aclandmark/PCB-111000_V2/9_Nano_Projects/7_Timers/7G_2_Combined_clock_SW/7G_2_Combined_clock_SW.ino

/*Proj_7G_Combined_clock_SW
***********************************************************/

/*IT INTRODUCES


  1.  A crystal controlled clock/Stop Watch application.

  Timing is provided using a 10mS I2C interrupt provided by the mini-OS that puts all clock/SW features under the
  control of the "Project_SW".
  The UNO clock has been found accurrate to about 1% which is not really adequate for monitoring the time.


  2.  An "atomic process".

  Elapsed time is recorded in seconds in a variable known as "sec_counter".  It is updated by a TWI ISR and processed
  by "main" and other subroutines. If any of these processes were interrupted by the TWI ISR then "sec_counter" would
  get corrupted and the process would fail.
  A different variable "sec_counter_V" is therefore defined.   This is the variable that the ISR updates directly.
  Its value is copied to "sec_counter" at regular intervals. Global interrupts are disabled while this process is
  in progress, using the following code

  " cli(); sec_counter = sec_counter_V; sei();"

  3.  Project subroutine "I2C_initiate_10mS_ref();"

  This is used to initiate the 10mS TWI interrupt


  EEPROM USAGE

  address 2 Data entry mode   Time string entered manually or seconds read from EEPROM
  addresses 3-6 Time input by user in seconds
  addresses 7-10 Display time time in secs (Clock or SW)
  addresses 11-14 "clock time" in seconds: When a new SW is selected save the "sec_counter" in clock time and
  "reset sec_counter"
  address 15 clock_mode


  USER INSTRUCTIONS



  Connect to pc  Should get "R   R   R   R....." user prompt
  if not hold sw2 down and reset.
  Keypress R gives the user insructions
  press sw3 get message enter time
  Enter time 24 hour clock
  Power cycle to 5V supply if wanted
  press sw3 then sw1 to start
  press sw1 to toggle between clock and new SW
  press sw2 to restore old SW
  press sw3 to pause, blank and restore display
  At initial POR press sw2 (rather that sw3) to get two SW's

  To adjust time: Press SW1 to restore clock time
  Then immediately press SW3
  This will cause a WD time out
  Release sw1 to increment time
  sw2 to decrement time
  Both switches to restore normal operation.


  Switch location SW1(PD2) - SW2(PD7) - SW3(PB2)
  PD2&7 call ISR(PCINT2_vect)
  PB2 calls ISR(PCINT0_vect)
  ISR on SW2 is never used.*/

/*
  clock_mode is storred in EEPROM address 2: When  subroutine set_time() is called
    users enter time for a clock_mode of 255 and mode is set thzero so that
    time is read from the EEPROM for a clock_mode of zero
    Having entered time set clock mode to zero
*/




#include "Proj_7G_2_header_file_1.h"
#include "Proj_7G_2_header_file_2.h"

long clock_time_secs = 0;                            //Value is seconds: Backed up in EEPROM when SW is selected


int main (void) {

  int line_no[6] = {0x14, 0x8B, 0xDE,  0x10F, 0x15F, 0x1C4};

  long SW_resume_time = 0;                              //Value in seconds: Used when switching from clock to SW
  long clock_resume_time = 0;                          //Value is seconds: Used when switching from SW to clock time


  /*****************Normal program entry mode: Everything is OK********************************/
  if (Arduino_non_WDTout) {                           //EEPROM 0x3EE holds anything except zero
    clear_Arduino_WDT_flag;                             //set it to to 0xFF

    setup_HW_for_clock_SW;

    Timer_T1_sub(T1_delay_100ms);
    if ((switch_2_down) || (MCUSR & (1 << EXTRF)))
    { while (switch_2_down); clear_data_mode;              //Ensure that the user prompt is skipped
      Timer_T1_sub(T1_delay_100ms);
    }

    else set_data_mode;


    if (data_mode_not_set)                              //Goes here following POR
    {if (power_on_reset == 1)
    {power_on_reset = 0;User_prompt_A;}
      Serial.write("\r\n\r\nTo retrieve these instructions press -r-\
at the p/r prompt or POR with sw2 pressed.\r\n\r\n\
Press sw3 and enter time or sw2 to reset it to zero,\
then press sw1 to start the clock.\r\n");
      for (int m = 0; m < 6; m++)
        Read_user_instructions(line_no[m]);//Serial.write(message_1);
    }

    for (int m = 0; m <= 11; m++)
    {
      eeprom_write_byte((uint8_t*)(m + 7), 0); //clear BKP space
    }

    while (1) {
      if (switch_2_down)
      {
        clock_mode = 2;  //Select timer or clock
        break;
      }
      if (switch_3_down) {
        clock_mode = 1;
        break;
      }
    }
    while ((switch_3_down) || (switch_2_down));

    clock_time_secs = 0;
    old_clock_mode = 0;
    payload = 2;
  }



  /*****************WDT with interrupt sets "Arduino_WDTout" and is used to adjust time**********************/
  if (Arduino_WDTout) {                                     //Arduino_WDTout
    clear_Arduino_WDT_flag;

    setup_HW_for_clock_SW;

    sec_counter = eeprom_read_byte((uint8_t*)(10));           //Read saved value of sec_counter from EEPROM
    for (int m = 0; m < 3; m++) {
      sec_counter = (sec_counter << 8)
                    + eeprom_read_byte((uint8_t*)(9 - m));
    }

    if ((switch_3_down) && (switch_1_down)) {                 //User induced watch dog timeout:
      while ((switch_3_down) || (switch_1_down)) {              //Use sw_1 and sw_3 to adjust time
        if ((switch_3_up) && (switch_1_down)) {
          sec_counter += 1;
        }
        if ((switch_1_up) && (switch_3_down)) {
          sec_counter -= 1;
        }
        Timer_T0_10mS_delay_x_m(10);
        Calculate_time();
        digits[0] = '0'; digits[1] = '0';                         //Sets mS*10 to zero  masks mS*10
        I2C_Tx_8_byte_array(digits);
      }
    }                            //Displays time as adjusted by user

    clock_mode = eeprom_read_byte((uint8_t*)15);              //Obtain "mode" and "clock_time_secs" from EEPROM
    clock_time_secs = eeprom_read_byte((uint8_t*)(14));
    for (int m = 0; m < 3; m++) {
      clock_time_secs = (clock_time_secs << 8) +
                        eeprom_read_byte((uint8_t*)(13 - m));
    }

    sec_counter += 1;                                     //Fudge factor??
    clock_resume_time = sec_counter;
    sec_counter_V = sec_counter;                          //Volatile version of "sec_counter"
    ms_counter = 0;                                       //mSecs are not restored
    clock_time_long = clock_time_secs * 100;
    Calculate_time();
    payload = 8;                                          //After WDT out update display
    setup_64ms_WDT_with_interrupt;                        //Re-establish WDT
    I2C_initiate_10mS_ref(); sei();
  }                       //Reinitialise 10mS tick


  /**************************Normal program continues********************************/
  set_up_PCI;
  enable_PCI;

  disable_PCI_on_sw1;
  disable_PCI_on_sw2;
  display_clear = 0;

  while (1) {                                               //Main loop: Continuously cycles through this loop (every 188uS??).

    switch (clock_mode) {
      case 0: break;
      case 1: set_time();                                       //Clock mode: "set_time()" requests start time  & saves it in "sec_counter"
        clock_mode = 'A'; break;
      case 2: sec_counter = 0;                                  //SW mode: start at time zero
        clock_mode = 'A';
        set_data_mode;
        for (int m = 0; m <= 3; m++)                          //Clear EEPROM sec_counter value
        {
          eeprom_write_byte((uint8_t*)(m + 3), 0);
        }
        break;
      case 'A':
        ms_counter = 0;
        sec_counter_V = sec_counter;                           //Initialise sec_counter_V
        Calculate_time();                                      //Converts time in seconds to string (Hr,Min and Sec)
        digits[0] = '0'; digits[1] = '0';                      //Sets mS*10 to zero  masks mS*10
        I2C_Tx_8_byte_array(digits);                           //Displays time
        clock_resume_time = sec_counter;
        clock_mode = 'E';
        break;

      case 'E':                                               //Clock ready to start: Awaiting sw3 press
        if (switch_1_up); else {
          I2C_initiate_10mS_ref();                              //Initiate TWI interrupt (every 10mS)
          sei();
          clock_mode = 'B';
          setup_64ms_WDT_with_interrupt;
        }                       //User input finished: Start WDT
        break;

      case 'B': if (!(TWI_flag));
        else {
          TWI_flag = 0; Update_sec_counter;                  //Clock running mode
          old_clock_mode = 'B';
          if (((86400 + sec_counter - clock_resume_time) % 86400 > 1)
              && ((switch_2_down) || (switch_1_down)))
          { if (switch_1_down) {
              clock_time_secs =
                clockTOstop_watch(); clock_mode = 'F';
            }
            if (switch_2_down) {
              SW_resume_time =
                restore_stop_watch(); clock_mode = 'H';
            }
          }
          else Timer();
        }
        break;                                                   //Convert clock to stop watch

      case 'F': if (!(TWI_flag));
        else {
          TWI_flag = 0; Update_sec_counter;                  //Stop watch mode
          old_clock_mode = 'F';
          if (((sec_counter) > 1) && ((switch_1_down)))
          {
            clock_resume_time = restore_Clock();
            clock_mode = 'B';
          }
          else Timer();
        }
        break;                                                  //Restore clock

      case 'H': if (!(TWI_flag));
        else {
          TWI_flag = 0;   Update_sec_counter;               //Stop watch restored mode
          old_clock_mode = 'H';
          if (((86400 + sec_counter - SW_resume_time) % 86400 > 1) &&
              (switch_1_down))
          {
            clock_resume_time = restore_Clock();
            clock_mode = 'B';
          }
          else Timer();
        }
        break;

      case 'C':
        payload = 0; TWI_flag = 0;
        Update_sec_counter; break;                              //Stop watch/clock display paused: Tick continues

      case 'G':
        payload = 0; TWI_flag = 0; Update_sec_counter;
        if (!(display_clear)) clear_display(); break;           //blank display

      case 'D':
        TWI_flag = 0;
        restore_display();  clock_mode = old_clock_mode;       //Stop watch/clock display re-activated
        break;
    }

    Timer_T2_sub(T2_delay_2ms);
    wdr();
  }
}                                               //reset the watchdog


/*****************************************************************************************************************/
void Timer(void) {                                     //Calls "update_7_seg_display", to close one I2C transaction and sets "payload" to initiate the next one
  digits[1] = ms_counter / 10 + '0';                    //Calculate mS display MSB
  digits[0] = ms_counter % 10 + '0';                    //Calculate mS display LSB
  if (!((digits[0] == '0') && (digits[1] == '0')))      //For mS tick 0 to 99 only update mS display
  {
    update_7_seg_display(); //Update mS display
  }
  if (!(ms_counter % 100)) {                            //When 1 second tick occurs
    Calculate_time();                                     //Calculate time: Hr:Min:Sec
    update_7_seg_display();
  }                              //Update display and complete the current I2C transaction
  if (ms_counter == 99)payload = 8; else payload = 2;
}       //Set payload for next TWI_interrupt 8 for 1sec tick, 2 for 10mS tick


/*****************************************************************************************************************/
ISR(TWI_vect) {                                         //Detects 10mS interrupt. Initiates I2C_transaction and responds by sending payload size
  unsigned char Null_byte;
  TWI_flag = 1;                                           //Informs main loop that a 10mS tick has occurred
  ms_counter = (ms_counter + 1) % 100;                    //mS counter continuously cycles through 0 to 100
  if (!(ms_counter)) {
    sec_counter_V++;                     //Volatile version of "sec_counter" increments every second
    if (sec_counter_V == 86400)sec_counter_V = 0;           //Roll-over for 24 hour clock
    sec_counter_save = 1;
  }                                     //Enables "sec_counter" to be updated from "sec_counter_V"
  Null_byte =  TWDR;                                       //Detect slave address + slave transmit data command
  TWDR = payload;                                          //Transmit payload value
  TWCR = (1 << TWEN) | (1 << TWINT);                       //clear interrupt but no ack required Next byte will be the last
  while (!(TWCR & (1 << TWINT)));                          //Wait for TWINT flag
  if (!(payload))
    TWCR =
      (1 << TWINT) | (1 << TWEA) | (1 << TWEN) | (1 << TWIE);
} //No payload? Prepare for next 10ms interrupt


/*****************************************************************************************************************/
void update_7_seg_display(void) {
  unsigned char Null_byte;
  cli();                                                    //Pause twi interrupt
  hold_PCI_on_sw1_and_sw3;
  {
    digits[0] = digits[1];  //Optional: masks 10mS digit
    digits[1] = 0;
  }
  TWCR = (1 << TWINT) | (1 << TWEA) | (1 << TWEN);         //Enable slave mode and set Enable Acknowledge
  while (!(TWCR & (1 << TWINT)));                          //No interrupt: wait for comms from master
  Null_byte =  TWDR;                                       //Read slave adress
  for (int m = 0;  m < payload; m++) {
    TWDR = digits[m];                                         //Transmit data for display
    if (m == (payload - 1))TWCR = (1 << TWINT) | (1 << TWEN); //last byte being transmitted now expect NACK in response
    else {
      TWCR = (1 << TWINT) | (1 << TWEA) | (1 << TWEN); //ACK pulse normally required
    }
    while (!(TWCR & (1 << TWINT)));
  }                          //Clear interrupt
  TWCR =
    (1 << TWINT) | (1 << TWEA) | (1 << TWEN) | (1 << TWIE);   //Prepare for next 10ms interrupt
  restore_PCI_on_sw1_and_sw3;
  sei();
}                                                   //re-enable twi interrupt


/*****************************************************************************************************************/
void Calculate_time(void) {
  Hours = sec_counter / 3600;                               //Obtain hours 0 to 23
  Minutes = (sec_counter % 3600) / 60;                      //Obtain minutes
  Seconds = (sec_counter % 3600) % 60;                      //Obtain seconds
  timer_utoa(Hours); HoursH = charH; HoursL = charL;        //Convert hours to string
  timer_utoa(Minutes); MinsH = charH; MinsL = charL;       //Convert minutes to string
  timer_utoa(Seconds); SecsH = charH; SecsL = charL;
}     //Convert seconds to string


/*****************************************************************************************************************/
void set_time(void) {
  unsigned int Two_sec_counter;                             //Required because of difficulties combining long and char variables
  unsigned char data_mode;

  data_mode = eeprom_read_byte((uint8_t*)0x02);             //Read mode. Default value is 255
  switch (data_mode) {

    case 255:                                                  //Default mode: User enters time
      Serial.write("\r\nEnter start time Hours, Minutes and \
Seconds (24 hour clock, no spaces)\r\n");
      while (isCharavailable_A(50) == 0) {
        Serial.write("T?  ");
      }
      HoursH = Serial.read();
      while (isCharavailable_A(5) == 0); HoursL = Serial.read();
      while (isCharavailable_A(5) == 0); MinsH = Serial.read();
      while (isCharavailable_A(5) == 0); MinsL = Serial.read();
      while (isCharavailable_A(5) == 0); SecsH = Serial.read();
      while (isCharavailable_A(5) == 0); SecsL = Serial.read();
      msecsH = 0; msecsL = 0;
      Two_sec_counter = ((((HoursH - '0') * 10) + HoursL - '0') * 1800)\
                        + ((((MinsH - '0') * 10) + MinsL - '0') * 30) + ((SecsH - '0') * 10 + SecsL - '0') / 2;
      sec_counter = Two_sec_counter;
      sec_counter *= 2;
      if (((SecsH - '0') * 10 + SecsL - '0') % 2)sec_counter++;

      for (int m = 0; m <= 3; m++)
      { eeprom_write_byte((uint8_t*)(m + 3), sec_counter >> (m * 8));
        Timer_T0_sub(T0_delay_5ms);
      }
      set_data_mode;
      break;

    case 0:
      sec_counter = eeprom_read_byte((uint8_t*)(6));          //Read start time and place in sec_counter
      for (int m = 0; m < 3; m++) {
        sec_counter = (sec_counter << 8) +
                      eeprom_read_byte((uint8_t*)(5 - m));
      }
      clear_data_mode;  break;

    default: clear_data_mode;
      wdt_enable(WDTO_30MS);
      while (1); break;
  }
}                                          //Corrupt clock_mode variable: set to default value and restart


/*****************************************************************************************************************/
void timer_utoa(char n) {                                   //converts an unsigned number to a string of digits
  if (n >= 10)
  { charL = n % 10;
    charH = (n - charL) / 10;
    charL = charL + '0';
    charH = charH + '0';
  }
  else
  {
    charH = '0';
    charL = n + '0';
  }
}


/*****************************************************************************************************************/
ISR(PCINT2_vect) {                                          //PORTB switch_1 interrupts

  if (switch_3_up)return;                                     //Ignore interrupt on switch release
  if (switch_1_up) {                                          //User triggered WDTout to adjust clock

    switch (clock_mode) {
      case 0: clock_mode = 1; break;                             //Enter the start timer
      case 'H':
      case 'F':
      case 'B':  clock_mode = 'C'; break;                         //Mode B clock is running Mode C Display paused
      case 'C':  clock_mode = 'G'; break;
      case 'G':  clock_mode = 'D'; break;
    }
  }

  else

    if (clock_mode != 'B')return;
    else {
      payload = 8; sei(); while (1);
    }
}


/*****************************************************************************************************************/
long clockTOstop_watch(void) {                             //Saves time before selecting stop watch display (i.e. resetting time to zero)
  long clock_time_secs_L;
  clock_time_long = (sec_counter * 100) + ms_counter;       //Current time "secs*10 + ms" saved in global variable clock_time.
  ms_counter = 0;                                           //Reset msecs
  sec_counter = 0;                                          //Reset secs
  clock_time_secs_L = clock_time_long / 100;                //Ignore ms when saving clock time
  update_7_seg_display();                                   //Runs "update_7_seg_display()" to complete the current I2C transaction
  payload = 8;                                              //Set payload to 8 for full display update during next I2C transaction
  while (!(ms_counter));                                    //Wait for next interrupt ms_counter increments from 0 to 1
  TWI_flag = 0;                                             //Clear TWI_flag
  for (int m = 0; m <= 7; m++)digits[m] = '0';              //Clears all digits
  update_7_seg_display();                                   //Runs "update_7_seg_display()" to complete I2C transaction
  payload = 2;                                              //Payload of 2 required for next update
  cli(); sec_counter_V = 0; sei();                          //Update volatile version of the sec_counter and return to "main loop"
  return clock_time_secs_L;
}


/*****************************************************************************************************************/
long restore_Clock(void) {                                 //Restores time by adding "clock_time" to the current SW time
  long time, clock_restore_time;
  unsigned char x;
  time = (sec_counter * 100) + ms_counter +
         clock_time_long;                                           //Add saved "clock_time" to SW time to get current value of time
  sec_counter = time / 100;                                  //Calculate new value of "sec_counter" and "ms_counter"
  ms_counter = time % 100 - 2;                               //2mS fudge factor required for mseconds
  if (sec_counter >= 86400)sec_counter -= 86400;            //compensates for 24Hr roll-over
  update_7_seg_display();                                   //Run "update_7_seg_display()" to complete the current I2C transaction
  x = ms_counter;                                           //Record "ms_counter"
  clock_restore_time = sec_counter;                         //saves "sec_counter" in "clock_restore_time"
  Calculate_time();                                          //Calculate time Hr:Min:sec
  digits[1] = ms_counter / 10 + '0';                         //Calculate mS display MSB
  digits[0] = ms_counter % 10 + '0';                         //Calculate mS display LSB
  payload = 8;                                               //Sets the payload to 8 ahead of next I2C transaction (update full disdplay)
  while (ms_counter == x);                                   //Wait for next interrupt (ms_counter increments from x to x+1)
  TWI_flag = 0;                                              //Set TWI_flag to zero
  update_7_seg_display();                                    //Full display update (completes the current I2C transaction)
  if (ms_counter == 99)payload = 8; else payload = 2;        //Enables contiguous 8 digit updates when necessary
  cli(); sec_counter_V = sec_counter; sei();                 //Update volatile version of second_counter
  Serial.write("\r\n"); return clock_restore_time;
}          //Return "clock_restore_time" to "main loop"


/*****************************************************************************************************************/
long restore_stop_watch() {                               //Restores SW time by subtracting the current time from the value stored in "clock_time"
  unsigned long time, SW_restore_time;
  unsigned char x;
  time = 8640000 + (sec_counter * 100) +
         ms_counter - clock_time_long;                            //Computes the updated value of SW time
  if (time >= 8640000) time -= 8640000;                    //Compensate for 24 Hr roll-over
  sec_counter = time / 100;                                //Calculate new value of "sec_counter" and "ms_counter"
  ms_counter = time % 100 - 2;                             //2mS fudge factor required for mseconds
  update_7_seg_display();                                  //Run "update_7_seg_display()" to complete the current I2C transaction
  x = ms_counter;                                          //Record "ms_counter"
  SW_restore_time = sec_counter;                           //saves "sec_counter" in "SW_restore_time"
  Calculate_time();                                        //Calculate time Hr:Min:sec
  digits[1] = ms_counter / 10 + '0';                       //Calculate mS display MSB
  digits[0] = ms_counter % 10 + '0';                       //Calculate mS display LSB
  payload = 8;                                             //Sets the payload to 8 ahead of next I2C transaction (update full disdplay)
  while (ms_counter == x);                                 //Wait for next interrupt (ms_counter increments from x to x+1)
  TWI_flag = 0;                                            //Clear TWI_flag
  update_7_seg_display();                                  //Full display update (completes the current I2C transaction)
  if (ms_counter == 99)payload = 8; else payload = 2;      //Enables contiguous 8 digit updates when necessary
  cli(); sec_counter_V = sec_counter;  sei();              //Update volatile version of the sec_counter
  return SW_restore_time;
}                                  //Return "SW_restore_time" to "main loop"


/*****************************************************************************************************************/
void restore_display(void) {                              //Re-activate Stop watch/clock display
  int x;
  { Calculate_time();                                        //calculate time in Hours, mins and secs
    x = ms_counter;                                           //Prepare to wait for next interupt
    payload = 8;                                              //Full display to be updated at next I2C transaction
    while (ms_counter == x);                                  //Wait for next interrupt
    update_7_seg_display();                                   //Update display: I2C expects a transfer of 8 bytes
    if (ms_counter == 99)payload = 8; else payload = 2;       //Set payload for next interrupt
    TWI_flag = 0;                                             //Clear TWI flag
    display_clear = 0;
  }
}                                     //Resets global variable "display_clear"


/*****************************************************************************************************************/
void clear_display(void) {                               //Blanks the display
  unsigned char x;
  display_clear = 1;                                       //sets global variable "display_clear"
  for (int m = 0; m <= 7; m++)digits[m] = 0;               //Clears all digits
  x = ms_counter;                                          //records current value of "ms_counter"
  payload = 8;                                             //Prepare for full display ubdate at next interrupt
  while (ms_counter == x);                                 //Wait for next interrupt ("ms_counter" increments to x+1)
  TWI_flag = 0;                                            //Reset "TWI_flag"
  update_7_seg_display();
}                                //Complete I2C_transaction



/*****************************************************************************************************************/
ISR (WDT_vect) {                                         //the clock often crashes when the display
  set_Arduino_WDTout;                                       //is being switch between stationary and blank
  for (int m = 0; m <= 3; m++)                              //WDTouts are also used to adjust the clock
  { eeprom_write_byte(((uint8_t*)(7 + m)),
                      (sec_counter >> (m * 8)) );
  }

  switch (clock_mode) {                                     //Save mode
    case 'B':
    case 'F':
    case 'H':
      eeprom_write_byte((uint8_t*)(15), clock_mode);
    case 'C':  case 'G': case 'D': eeprom_write_byte((uint8_t*)(15), old_clock_mode);
    default: break;
  }

  for (int m = 0; m <= 3; m++)
  {
    eeprom_write_byte(((uint8_t*)(11 + m)), (clock_time_secs >> (m * 8)) );
  }
}


/***********************************************************************************************************************/
void Read_user_instructions(int EEPROM_address) {
  char temp_char;

  newline_A();
  while (1) {
    temp_char =  eeprom_read_byte((uint8_t*)(EEPROM_address++));
    if (temp_char != '\0') Serial.write(temp_char);
    else {
      newline_A();
      break;
    }
  }
}




/*************************************************************************************************************************************/
