aclandmark/PCB-111000_V2/9_Nano_Projects/5_Arduino_PC_comms_library/5A_Integer_numbers/5A_Integer_numbers.ino

/*
 At this point a template for Arduino programs is developed. 
 
 Some Arduino and standard C library functions are introduced and used.
 For example 
 Serial.begin(115200):    This initialises the UART for 57600 Baud (assuming an 8MHz clock)
 Serial.write:            This sends text to the PC
 Serial print:            This sends numbers to the PC as text
 atol/atoi:               C functions that convert a text string to a long / integer number
 ltoa:                    C function that converts a long number to text (askii characters)

 Note all characters received by the UART are saved to a buffer.
 Serial.readBytesUntil as implemented here reads these characters and transfers them
 to a separate buffer "num_as_string" stopping only when a cartridge return (cr) is detected
 or a defined number keypresses have been made (i.e. 20 or 30).
 The keypresses contained in the buffer "num_as_string" are then converted to a number. 
 

 The reason for resets is determined. Four resets are considered; these are
	POR (power on reset)
	WDT	(watch dog timeout) used to generate  a planned or soft ware reset (SW_reset)
	WDT with flag: Like the WDT but the code writes to the EEPROM immediately before the reset
	Ext Reset: 	Only generated by a keypress -r- at the "p/r   p/r...." prompt for these projects 
	
	For battery applications a BOR brown out reset can also be detected though these have not been implemented here.

At a later stage the WDT with interrupt will also be introduced. Here this is used is to reset programs 
preventing them from going unresponsive due to unexpected inputs or switch presses. All subroutines especially those 
involving keyboard input should be made WD proof with the wdr() command. This resets the WD timer and prevents a reset. 

This project accepts an integer number and prints out all the integer numbers by which it can be divided
 giving an integer result.
 
Subroutines Int_Num_to_PC_A and Int_Num_from_PC_A() can be found in  UNO_proj_resources\PC_comms\Arduino_Rx_Tx_UNO_pcb.c
Int_Num_from_PC_A() implements the backspace key press

*/
/*
EEPROM usage
0x1FF, 0x1FE and 0x1FD     OSCCAL
0x1FC and 0x1FB            PRN generator
0x1FA                      Reset source
 */


/************************************************************************************************************/
#include "Integer_numbers_header.h"

#define message_1 "\r\nEnter integer number:  PCB returns all factors of that number.(Press sw1 to cancel.)\r\n"
#define message_2 "New number?\r\n"
#define message_3 "\r\nCalculation cancelled. New number?\r\n"


#define BL 30                     //Buffer length

int main (void)  
  { 
    char num_string[BL + 2];
    long  num;
    long m = 1;
 
 setup_HW_Arduino;
 set_up_pci_on_sw1_and_sw3;
 enable_pci_on_sw1_and_sw3
 
switch(reset_status){
  case POR_reset:                 User_prompt_A;    Serial.write(message_1);break;
  case WDT_reset:                 Serial.write(message_2);break;
  case WDT_reset_with_flag:       Serial.write(message_3);break;
  case External_reset:            Serial.write(message_1);break;}
 
num = Int_Num_from_PC_A_Local(num_string,BL);

newline_A();
Serial.print(num);
Serial.write("\t");

do{
if(!(num%m)){Int_Num_to_PC_A_Local(m, num_string, '\t');}
m += 1; if(!(m%10000))Serial.write(".");}while(m < num);

SW_reset;
return 1;  }





/******************************************************************************************/
long Int_Num_from_PC_A_Local(char * num_as_string, char bufferlen)    //Project version implements the backspace key
{char strln;
Serial.flush();   
strln = Serial.readBytesUntil('\r',num_as_string, bufferlen);
num_as_string[strln] = 0;
return atol(num_as_string);}



/******************************************************************************************/
void Int_Num_to_PC_A_Local(long Int_num, char * num_as_string, char next_char)
{ltoa(Int_num, num_as_string, 10);
Serial.print(num_as_string);
Serial.print(next_char);}


ISR(PCINT2_vect){
if(switch_3_down) return;
if((switch_1_up) && (switch_3_up))return;
 if(switch_1_down) eeprom_write_byte((uint8_t*)0x1FA, 0);
 SW_reset;}


/******************************************************************************************/
