aclandmark/PCB-111000_V2/9_Nano_Projects/5_Arduino_PC_comms_library/5B_Prime_factors/5B_Prime_factors.ino

/*
 As 5A but accepts an integer number and converts it to its prime factors
 See project "3F_Prime_numbers" for an intruction to prime numbers
 */

/*
EEPROM usage
0x1FF, 0x1FE and 0x1FD     OSCCAL
0x1FC and 0x1FB            PRN generator
0x1FA                      Reset source
*/


#include "Prime_factors_header.h"

#define message_1 "\r\nEnter integer number:  PCB returns all prime factors of that number.(Press sw1 to cancel.)\r\n"
#define message_2 "New number?\r\n"
#define message_3 "\r\nCalculation cancelled. New number?\r\n"


#define Search_array_length   125

#define BL 30                     //Buffer length

/************************************************************************************************************/
int main (void)  
  { 
    char num_string[BL + 2];
    long  number;
    long factor;
    char factor_counter;
 
 setup_HW_Arduino;
set_up_pci_on_sw1_and_sw3;
 enable_pci_on_sw1_and_sw3

switch(reset_status){
  case POR_reset:                 User_prompt_A;    Serial.write(message_1);break;
  case WDT_reset:                 Serial.write(message_2);break;
  case WDT_reset_with_flag:       Serial.write(message_3);break;
  case External_reset:            Serial.write(message_1);break;}

  
   number = Int_Num_from_PC_A_Local(num_string, BL);
   newline_A();
  Serial.print(number);  _delay_ms(5);

  Serial.write('\t');
  factor_counter = 0;
  do{_delay_ms(5);                                                  //Required by Serial.print
  factor = Product_search(number);                                 //Get lowest factor
  number = number/factor;                                          //Next number to factorise
  Int_Num_to_PC_A(factor,num_string, '\t' ); //
  factor_counter += 1;} 
  while (number != 1);  

  if(factor_counter == 1){Serial.write("Prime\r");}
  SW_reset;
  return 1;}



/************************************************************************************************************/
long Product_search  (long number)  {
long search_array[Search_array_length]; 
int j=0;
long n=Search_array_length;
long L=0;

while(1){
for(long k =0; k < n; k++)                              //Populate array (i.e. with 401, 402, 403, ..etc) 
{search_array[k] = k+1+n*L;}
prime_no_generator(L,n,search_array);                   //Set all non primes in array to zero
j=0; 
while(search_array[j] == 0)j += 1;                     //Select first prime number
while (j<=Search_array_length)
{if ((search_array[j] >= 2) &&
(number%search_array[j] == 0))                         //Scan array until a factor is found
{return search_array[j];}                              //and return it
j += 1;} 
if(L*Search_array_length > number)return 0;                            //No factors found at all: Return zero for prime number
L += 1; Serial.write('.');}}                           //No factor found in array: increment L and populate new array



/************************************************************************************************************/
void prime_no_generator
(long L, long n,  long reg[]){                  //n the array size is 200, I is the array number (zero for the first one)
  
long i;                                         //We compute the product i * m
long m;                                        //i always starts at 2 then increments to 3, 4, etc.
i=2;                                           //m is set to take us to the beginning of the array 
while (i*i < n*(L+1)){                         //Maximum value i can take
wdr();
m=0;
while(i*(i+m) <= n*L)m++;                      //Go to start of the new array for example
while(i*(i+m) <= n*(1+L))                      //2*101, 2*102, 2*103,... etc   3*67,3*68, 3*69,...etc    5*41, 5*42,...etc
{reg[i*(i+m) -1 - n*L] = 0; m++;wdr(); }      //set appropriate registers to zero (Note the offset of 1 place) 
i++;}}


/************************************************************************************************************/
ISR(PCINT2_vect){
if(switch_3_down) return;
if((switch_1_up) && (switch_3_up))return;
 if(switch_1_down) eeprom_write_byte((uint8_t*)0x1FA, 0);
 SW_reset;}



/************************************************************************************************************/
long Int_Num_from_PC_A_Local(char * num_as_string, char bufferlen)    //Project version implements the backspace key
{char strln;
Serial.flush();   
strln = Serial.readBytesUntil('\r',num_as_string, bufferlen);
num_as_string[strln] = 0;
return atol(num_as_string);}



/************************************************************************************************************/
