aclandmark/PCB-111000_V2/9_Nano_Projects/3_Interrupts_and_switches/3D_timer_PCI_interrupts/3D_timer_PCI_interrupts.ino

/*
 Timer interrupts drive the display with any one of three patterns
 User switch SW1, 2 or 3 are used to select which one.
 
 Three interrupts are active:
 the timer, the one wire comms and PCI
 To simplify operation the PCI ISR resets the Atmega328.
 However before doing this it writes to the EEPROM.
 EEPROM is special memory the survives reset.
 The first thing the program does following a reset is to 
 read the EEPROM to determine which pattern is required.
 */


#include "Timer_PCI_header.h"
volatile char T1_COMP;
unsigned int n, n_max;
long PORT_1, PORT_2;
char p = 0;
char mode = 1;


/************************************************************************/
int main (void)
{ setup_HW;
 _delay_ms(10);
 sei();
 
  mode = eeprom_read_byte((uint8_t*)0);

  switch (mode)
  { case 0: case 1: case 2: break;
    default: mode = 0; break;
  }
  set_up_PCI;
  enable_pci;
  T1_COMP = 0;
  
  T1_100ms_clock_tick();
  initialise_display();
  while (1)
  { while (!(T1_COMP)); T1_COMP = 0;
    Inc_Display();
  }
}


/************************************************************************/
ISR(TIMER1_COMPA_vect)
{ 
  OCR1A += 0x30D4;
  T1_COMP = 1;
}


/************************************************************************/
ISR(PCINT2_vect)
{ if ((switch_1_up) && (switch_2_up) && (switch_3_up)) {
    return;
  }
  if (switch_3_down) eeprom_write_byte((uint8_t*)0x0, 0);
  if (switch_1_down) eeprom_write_byte((uint8_t*)0x0, 1);
 
  SW_reset;
}


/************************************************************************/
ISR(PCINT0_vect)
{ if ((switch_1_up) && (switch_2_up) && (switch_3_up)) {
    return;
}

if (switch_2_down) eeprom_write_byte((uint8_t*)0x0, 2);
SW_reset;
}



/************************************************************************/
void T1_100ms_clock_tick(void)
{ TCNT1 = 0;
  OCR1A = 0x30D4;
  TIMSK1 |= (1 << OCIE1A);
  TCCR1B = 0x03;
}


/************************************************************************/
void initialise_display()
{ n = 1;
  PORT_1 = 1;
  PORT_2 = 0x8000;
  switch (mode)
  { case 0: n = 0; PORT_1 = 1 << p;
      PORT_2 = 0x8000 >> p; n_max = 16 - (2 * p); break;
    case 1:  n_max = 17; break;
    case 2: n_max = 16; break;
  }
 I2C_Tx_2_integers(PORT_1, PORT_2);
}



/************************************************************************/
void Inc_Display()
{ switch (mode)
  { case 0: PORT_1 = PORT_1 << 1;
      PORT_2 = PORT_2 >> 1; break;

    case 1:
      if (n < 8)
      { PORT_1 |= (1 << (2 * n));
        PORT_2 |= (0x8000 >> (2 * n));
      }
      else
      { PORT_1 = PORT_1 << 2;
        PORT_2 = PORT_2 >> 2;
      } break;

    case 2: if (n < 5)
      { PORT_1 |= PORT_1 << 1;
        PORT_2 |= PORT_2 >> 1;
      }
      else
      { PORT_1 = PORT_1 << 1;
        PORT_2 = PORT_2 >> 1;
      } break;
  }
  //One_wire_Tx_2_integers_with_timer_control(PORT_1, PORT_2);
  I2C_Tx_2_integers(PORT_1, PORT_2);
  
  n += 1;
  if (n == n_max)
  {
    n = 0;
    p += 1;
    p = p % 8;
    initialise_display();
  }
}






/*****************************************************************************************************************/
