aclandmark/PCB-111000_V2/9_Nano_Projects/8_Atmel_studio/Proj_8B_data_arrays/Proj_8B_data_arrays/Proj_8B_data_arrays.c

/*Proj_8B_data_arrays
***********************************************************************/

/*Puts the C maths library through its paces.

Data arrays are generated in a spreadsheet and then saved as .csv files.
As a file is downloaded the program keeps a running total of the sum and product of its numbers
At the end of the download the arithmetic and geometric means are calculated and sent to the PC.

Note: we slow the data rate down a bit because flow control has not been implemented.
*/




#include "Proj_8B_header.h"



/*************************Define input streams*************************************************************/
int uart_getfloat_from_csv(FILE *mystr_input);

FILE  uart_output = FDEV_SETUP_STREAM (uart_putchar, NULL, _FDEV_SETUP_WRITE);
FILE uart_input_any_char = FDEV_SETUP_STREAM(NULL, uart_getchar, _FDEV_SETUP_READ);
FILE uart_input_float_from_csv = FDEV_SETUP_STREAM(NULL, uart_getfloat_from_csv, _FDEV_SETUP_READ);


int num_counter;

int main(void)

{float Floating_point_num, accumulator_A, accumulator_G;

	setup_HW;
	
	if ((MCUSR & (1 << PORF)) || MCUSR & (1 << EXTRF)){MCUSR = 0;
		stdout = &uart_output;
		stdin  = &uart_input_any_char;
		printf("Select 9.6k baud rate, then AK to continue\r\n");Timer_T0_10mS_delay_x_m(1);
		setup_PC_comms_Basic(0,103);getchar();
		printf("Send data files\rArithmetic mean\tGeometric mean\t data items");
	SW_reset;}

	setup_PC_comms_Basic(0,103);
	while(1){
	num_counter = 0;
	stdout = &uart_output;
	stdin  = &uart_input_float_from_csv;
	accumulator_G = 0;
	accumulator_A = 0;
	while(1){scanf("%f", &Floating_point_num);
		if(!(Floating_point_num))break;
		accumulator_A += Floating_point_num;
	accumulator_G += log10(Floating_point_num);}
	binUnwantedChars();
	printf("\n%g  ", (accumulator_A/(num_counter-1)));
	printf("\t\t%g  ", pow(10,(accumulator_G/(num_counter-1))));
	printf("\t\t%d  ", (num_counter-1));}
	
	SW_reset;
return 0;}
	
		

/***********************************************************************************************************/
int uart_getfloat_from_csv(FILE *mystr_input)		
{char keypress;
	{while (!(UCSR0A & (1 << RXC0)));
		keypress = UDR0;
		while(!(decimal_digit_Basic (keypress)) && (keypress != '\r')
		&& (keypress != '\n')&& (keypress != '-')&& (keypress != '.')&& (keypress != '\t')
		&& (keypress != 'e') && (keypress != 'E')&& (keypress != ','))
		{while((isCharavailable_Basic(100) == 0));keypress = UDR0;}
		if ((keypress == ',') || (keypress == '\t')  || (keypress == '\r')){keypress = '\n';num_counter += 1;}
	return keypress;}}
	
	
	
/***********************************************************************************************************/	
	int uart_getchar_Local(FILE *mystr_input)									//Special version
	{int n = 0, m = 5;
		while (!(UCSR0A & (1 << RXC0)))
		{n++;																	//No character yet: Increment counter
			if (n>8000){m--;n = 0;}if (m == 0)return 0;}
		return UDR0;}
