aclandmark/PCB-111000_V2/Programmers/5_Project_pcb_168_V2.30_Arduino_V2/Project_pcb_168_V2.30_Arduino.h

#include <avr/io.h>
#include <stdlib.h>
#include <avr/interrupt.h>
#include <avr/wdt.h>
#include <avr/eeprom.h>


void Read_on_chip_EEPROM(int);
void USART_init (unsigned char, unsigned char);
void newline(void);
void Timer_T0_sub(char, unsigned char);
void Timer_T0_10mS_delay_x_m(int);
char waitforkeypress(void);
char receiveChar(void);
char isCharavailable (int);
void binUnwantedChars (void);
void sendChar(char);
void sendString(char*);
char Read_write_mem(char, int, char);
void Load_page(char, int, unsigned char);


#define prescaller_setting          2
#define RBL                         255

#define enable_PCI_on_SCK_pin       PCICR |= (1 << PCIE0);
#define set_PCI_mask_on_SCK         PCMSK0 |= (1 << PCINT5);
#define disable_PCI_on_SCK_pin      PCICR &= (~(1 << PCIE0));
#define clear_PCI_mask_on_SCK       PCMSK0 &= (~(1 << PCINT5));

#define two_msec_delay              Timer_T0_sub(T0_delay_2ms);
#define five_msec_delay             Timer_T0_sub(T0_delay_5ms);
#define ten_msec_delay              Timer_T0_sub(T0_delay_10ms);
#define twenty_msec_delay           Timer_T0_sub(T0_delay_20ms);

#define T0_delay_20ms                  5,100
#define T0_delay_10ms                  5,178
#define T0_delay_5ms                   5,220
#define T0_delay_2ms                   4,195

#define                           T0_delay_5ms 5,220
#define                           T0_delay_20ms 5,100


volatile int  EA_counter, EA_buff_ptr;
volatile long error_sum;
volatile long TCNT1_sum;
volatile char int_counter;
unsigned char OSCCAL_WV, OSCCAL_DV;
unsigned char OSCCAL_UV;
unsigned char osccal_MIN;
long          percentage_error;
char          cal_mode;
long          buffer[45];


#define inc_r_pointer \
r_pointer++;\
r_pointer = r_pointer & 0b00011111;


int  cmd_counter;											                    //Counts commands as they are downloaded from the PC
int prog_counter;											                    //Counts commands burned to flash
signed int  read_ops=0;										                //Total number of commands read from flash
volatile int counter;										                  //Counts characters in a record as they are downloded from the PC
volatile int char_count;									                //The number of askii character in a single record
volatile unsigned char Count_down;							          //Counts commands as record is programmed
volatile int   tempInt1, tempInt2;							          //Used to assemble commands and addresses as the are downloaded
int store[35];												                    //Used to store commands and address ready for the programmer
volatile unsigned char w_pointer,r_pointer;					      //Read/write pointers to "store" to which hex file is saved
unsigned int Hex_cmd;										                  //Command read from flash during verification

unsigned char cmd_pin, resp_pin, clock_pin, reset_pin;		//Used to define the programming pins

unsigned int target;
int Hex_address;											                    //Address read from the hex file
int HW_address;												                    //Hard ware address (usually tracks Hex_address)
signed int page_address;									                //Address of first location on a page of flash 
volatile int write_address;									              //Address on page_buffer to which next command will be written
signed int FlashSZ;											                  //Amount of flash memory supplied on target device
signed int PAmask;											                  //Used to obtain the flash page address from the hex address
signed int PageSZ;											                  //Size of a page of flash

signed char short_record;									                //Record  containing less that eight 16 bit commands
signed char page_offset;									                //Address of first location on page buffer to be used
signed char space_on_page;									              //Keeps a track of the space remaining on a page buffer
unsigned char Flash_flag;									                //Indicates that the page buffer contains commands

signed char record_length;
signed char record_length_old;
signed char orphan;											                  //Indicates that the contents of a record span two flash pages
signed char section_break;									              //Set to 1 if at least one page of flash memory will be unused.
signed char page_break;										                //Page only partialy filled before programming next one starts
volatile signed char line_offset;
unsigned int prog_led_control;


signed int EE_top;											                  //Max address available for user srings
char  cal_factor=0;											                  //1: Use call factor	0: default cal factor
int text_start, text_start_mem;								            //Controls writing user strings to rarget EEPROM
char watchdog_reset;										                  //Set to 1 when watchdog timeout occurs



/***************************************************************************************************************/
#define setup_HW \
setup_watchdog;\
OSCCAL_DV = OSCCAL;\
OSC_CAL;\
set_up_I2C;\
ADMUX |= (1 << REFS0);\
set_up_I_O;\
\
USART_init(0,16);\
Timer_T0_10mS_delay_x_m(5);\
Set_LED_ports;\
LEDs_off;



/***************************************************************************************************************/
#define wdr()  __asm__ __volatile__("wdr")

#define setup_watchdog \
if (MCUSR & (1<<WDRF)) watchdog_reset = 1;\
wdr();\
MCUSR &= ~(1<<WDRF);\
WDTCSR |= (1 <<WDCE) | (1<< WDE);\
WDTCSR = 0;\


/***************************************************************************************************************/
#define set_up_I2C TWAR = 0x02;



/***************************************************************************************************************/
#define OSC_CAL \
if ((eeprom_read_byte((uint8_t*)0x1FF) > 0x0F)\
&&  (eeprom_read_byte((uint8_t*)0x1FF) < 0xF0) && (eeprom_read_byte((uint8_t*)0x1FF)\
== eeprom_read_byte((uint8_t*)0x1FE))) {OSCCAL = eeprom_read_byte((uint8_t*)0x1FF);cal_factor=1;}



/***************************************************************************************************************/
void save_cal_values(unsigned char OSCCAL_user){
eeprom_write_byte((uint8_t*)(0x1FF), OSCCAL_user); 
eeprom_write_byte((uint8_t*)(0x1FE), OSCCAL_user); 
eeprom_write_byte((uint8_t*)(0x1FD), OSCCAL_DV);}



/***************************************************************************************************************/
#define set_up_I_O \
MCUCR &= (~(1 << PUD));\
DDRB = 0;\
DDRC = 0;\
DDRD = 0;\
PORTB = 0xFF;\
PORTC = 0xFF;\
PORTD = 0xFF;\
PORTC &= (~(1 << PC3));	



/***************************************************************************************************************/
#define Initialise_variables_for_programming_flash \
prog_counter=0;  prog_led_control = 0; cmd_counter = 0; record_length_old=0;\
Flash_flag = 0;  HW_address = 0;  section_break = 0; orphan = 0;\
w_pointer = 0; r_pointer = 0; short_record=0;\
counter = 1;



/***************************************************************************************************************/
#define Prog_enable 0xAC530000
#define Prog_enable_h 0xAC53

#define signature_bit_1 0x30000000
#define signature_bit_1_h 0x3000

#define signature_bit_2 0x30000100
#define signature_bit_2_h 0x3000
#define signature_bit_2_l 0x0100

#define signature_bit_3 0x30000200
#define signature_bit_3_h 0x3000
#define signature_bit_3_l 0x0200

#define read_fuse_bits 0x50000000
#define read_fuse_bits_h 0x5000

#define read_fuse_bits_H 0x58080000
#define read_fuse_bits_H_h 0x5808

#define read_lock_bits 0x58000000
#define read_lock_bits_h 0x5800

#define read_extended_fuse_bits 0x50080000
#define read_extended_fuse_bits_h 0x5008

#define write_lock_bits 0xACE00000
#define write_lock_bits_h 0xACE0

#define write_fuse_bits_H 0xACA80000
#define write_fuse_bits_H_h 0xACA8

#define write_fuse_bits 0xACA00000
#define write_fuse_bits_h 0xACA0

#define write_extended_fuse_bits 0xACA40000
#define write_extended_fuse_bits_h 0xACA4

#define Chip_erase 0xAC800000
#define Chip_erase_h 0xAC80


/***************************************************************************************************************/
#define PGD_cmd_H         PORTB |= cmd_pin
#define PGD_cmd_L         PORTB &= ~(cmd_pin)
#define PGD_resp_H        PINB & resp_pin
#define PGC_L             PORTB &= ~(clock_pin)
#define PGC_H             PORTB |= clock_pin
#define Reset_L           PORTC &= ~(reset_pin)
#define Reset_H           PORTC |= reset_pin

#define boot_target       cmd_pin =  0x08; resp_pin = 0x10; clock_pin =  0x20; reset_pin = 0x08; DDRB |= 0x28; DDRC |= 0x08;


/***************************************************************************************************************/
#define Set_LED_ports	  DDRB = (1 << DDB0) | (1 << DDB1);
#define LEDs_on         PORTB |= (1 << PB0)|(1 << PB1);
#define LEDs_off        PORTB &= (~((1 << PB0)|(1 << PB1)));
#define LED_1_on        PORTB |= (1 << PB1);
#define LED_1_off       PORTB &= (~( 1<< PB1));	
#define LED_2_off       PORTB &= (~(1 << PB0));
#define LED_2_on        PORTB |= (1 << PB0);



/***************************************************************************************************************/
#define Atmel_powerup \
{two_msec_delay;}\
Reset_L;\
PGC_L;\
{two_msec_delay;}\
Reset_H;\
{two_msec_delay;}\
Reset_L;\
{twenty_msec_delay;}

#define Atmel_powerup_and_target_detect \
Atmel_powerup;\
while(1){if((Atmel_config(Prog_enable_h, 0)==0x53) && (Atmel_config(signature_bit_1_h, 0) == 0x1E))break;\
else {sendString("TTND"); wdt_enable(WDTO_120MS);while(1);}}\
target_type_M = (byte)Atmel_config(signature_bit_2_h, signature_bit_2_l);\
target_type = (byte)Atmel_config(signature_bit_3_h, signature_bit_3_l);\
switch(target_type) {\
case 0x07: target = 8; break;\
case 0x08: target = 35; break;\
case 0x05:\
case 0x0A:\
if (target_type_M == 0x92) target = 48; else target = 88; break;\
case 0x14:\
case 0x0F: if(target_type_M == 0x95) {target = 328;sendChar('B');} else target = 88; break;\
case 0x06:\
case 0x0B: if(target_type_M == 0x94)target = 168; if(target_type_M == 0x93)target = 15;break;\
default: newline(); sendString("TTND"); newline(); wdt_enable(WDTO_120MS);while(1);break;}



/***************************************************************************************************************/
#define Text_Atmega                   newline(); Read_on_chip_EEPROM(0x0);
#define Text_detected                 Read_on_chip_EEPROM(0x8); newline();
#define Text_Press_P_or_E             Read_on_chip_EEPROM(0x12);newline();
#define Text_Send_HexF                newline(); Read_on_chip_EEPROM(0x5D); newline();
#define Text_EEP_reset                Read_on_chip_EEPROM(0x7E); newline();
#define Text_10_sec_wait              Read_on_chip_EEPROM(0x98);

#define Text_Config                   Read_on_chip_EEPROM(0xA4); newline();
#define Text_on_chip_cal              Read_on_chip_EEPROM(0xD5);
#define Text_File_size                newline(); Read_on_chip_EEPROM(0xE6);
#define Text_Auto_cal                 Read_on_chip_EEPROM(0xF6); newline();
#define Text_target_cal               newline();Read_on_chip_EEPROM(0x130);
#define Text__Press_W_or_R            newline(); Read_on_chip_EEPROM(0x149);

#define Text_Program_Verification     newline(); Read_on_chip_EEPROM(0x199);
#define Text_Baud_Rate_H              newline(); Read_on_chip_EEPROM(0x1CA); newline();




/***************************************************************************************************************/
#define User_prompt \
while(1){\
do{sendString("R?    ");}	 while((isCharavailable(250) == 0));\
User_response = receiveChar();\
if((User_response == 'R') || (User_response == 'r'))break;} sendString("\r\n");



/***************************************************************************************************************/
#define waiting_for_I2C_master \
TWCR = (1 << TWEA) | (1 << TWEN);\
while (!(TWCR & (1 << TWINT)));\
TWDR;


#define clear_I2C_interrupt \
TWCR = (1 << TWINT);



/***************************************************************************************************************/
#include "Resources/Project_pcb_168_V2.30_Arduino_SW_subs.c"
#include "Resources/Project_pcb_168_V2.30_Arduino_HW_subs.c"
#include "Resources/1_Basic_Timer_IO_subs.c"
#include "Resources/Project_pcb_168_V2.30_Arduino_EEPROM_subs.c"




/***************************************************************************************************************/
